oyetkin/droneiotclient/data_vis_demo/graph_images/arjun_station_humidity.jpg

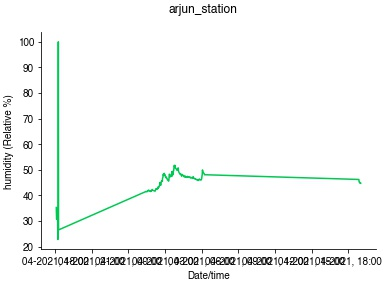
data_vis_demo/graph_images/arjun_station_humidity.jpg
