oyetkin/droneiotclient/data_vis_demo/graph_images/arjun_station_pressure.jpg

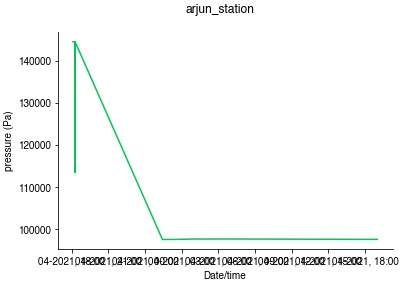
data_vis_demo/graph_images/arjun_station_pressure.jpg
