oyetkin/droneiotclient/data_vis_demo/graph_images/arjun_station_temperature.jpg

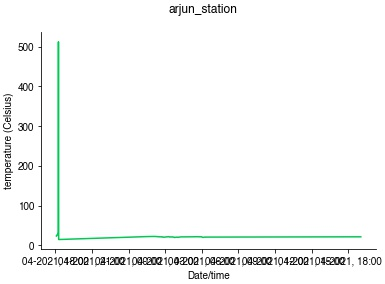
data_vis_demo/graph_images/arjun_station_temperature.jpg
