oyetkin/droneiotclient/data_vis_demo/graph_images/Arjun_weather_kit_pressure.jpg

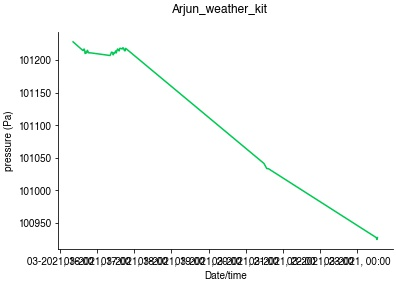
data_vis_demo/graph_images/Arjun_weather_kit_pressure.jpg
