oyetkin/droneiotclient/data_vis_demo/graph_images/Arjun_weather_kit_temperature.jpg

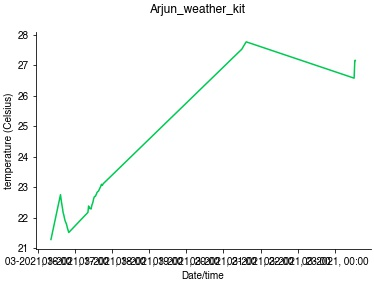
data_vis_demo/graph_images/Arjun_weather_kit_temperature.jpg
