oyetkin/droneiotclient/data_vis_demo/graph_images/Arjuns_kit_humidity.jpg

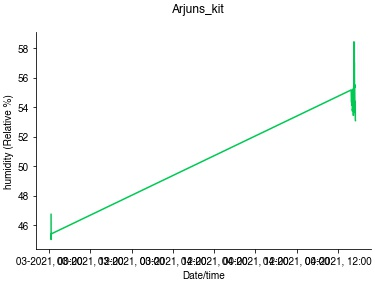
data_vis_demo/graph_images/Arjuns_kit_humidity.jpg
