oyetkin/droneiotclient/data_vis_demo/graph_images/Arjuns_kit_pressure.jpg

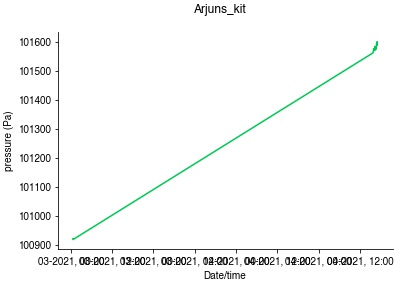
data_vis_demo/graph_images/Arjuns_kit_pressure.jpg
