oyetkin/droneiotclient/data_vis_demo/graph_images/josh_station2_humidity.jpg

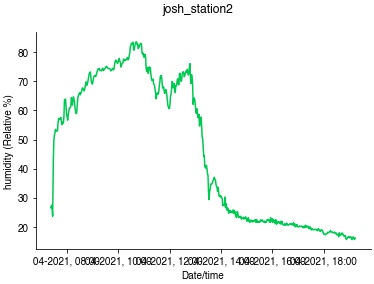
data_vis_demo/graph_images/josh_station2_humidity.jpg
