oyetkin/droneiotclient/data_vis_demo/graph_images/otto_stations_otticity.jpg

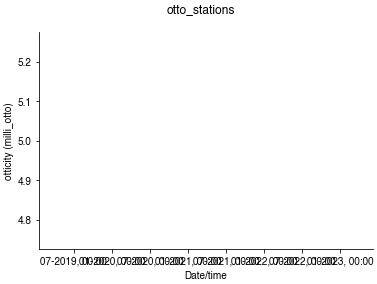
data_vis_demo/graph_images/otto_stations_otticity.jpg
