oyetkin/droneiotclient/data_vis_demo/graph_images/san_diego_5_.jpg

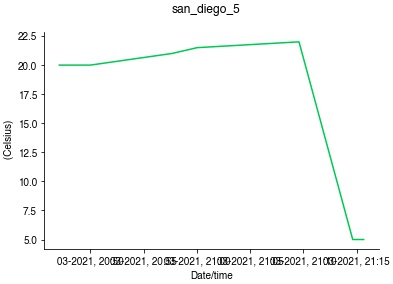
data_vis_demo/graph_images/san_diego_5_.jpg
