oyetkin/droneiotclient/data_vis_demo/graph_images/san_diego_6_.jpg

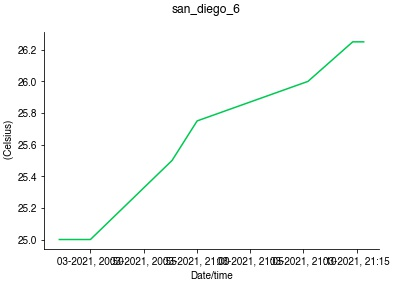
data_vis_demo/graph_images/san_diego_6_.jpg
