oyetkin/droneiotclient/pcb_data_logger_collector/pcb_data_logger_collector_footprint.png

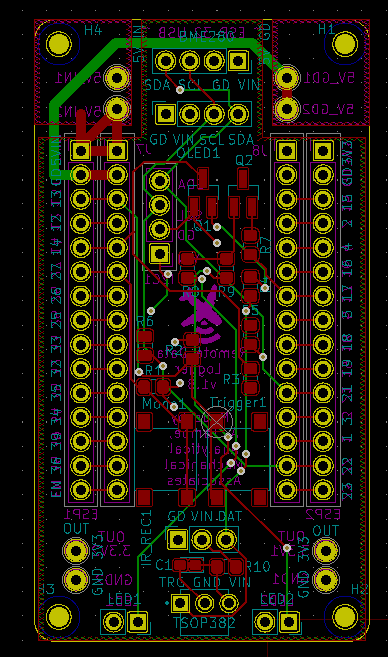
pcb_data_logger_collector/pcb_data_logger_collector_footprint.png
