oyetkin/droneiotclient/data_vis_demo/graph_images/arjun_test_temp_test.jpg

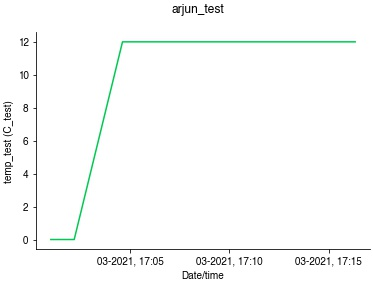
data_vis_demo/graph_images/arjun_test_temp_test.jpg
